ouras/STM32-Audio-Effects-Unit/board/LTspice/biased input amp with filter.asc

C1: cap; 1n
C2: cap; 10µ
C3: cap; 15µ
C4: cap; 1n
R1: res; 24k
R2: res; 220k
R3: res; 220k
R4: res; 1Meg
R5: res; 33k
R6: res; 2.4k
R7: res; 1.2k
U1: UniversalOpamp2
V1: voltage; 3.3
V2: voltage; ""; AC 100m 0
Named nets: 0, Vdd, out, in
.ac lin 1000 1 30k
