ouras/STM32-Audio-Effects-Unit/board/LTspice/output filter.asc

C1: cap; 2.2n
C2: cap; 10µ
C4: cap; 1n
R1: res; 4.3k
R4: res; 1Meg
R7: res; 3.3k
U1: UniversalOpamp2
V1: voltage; 3.3
V2: voltage; ""; AC 100m 0
Named nets: 0, Vdd, out, in
.ac lin 1000 1 30k
