ouras/STM32-Audio-Effects-Unit/board/LTspice/power.asc

D1: schottky
D2: schottky
M1: pmos
R1: res; 10k
R2: res; 1k
V1: voltage; 9
V2: voltage; 9
V3: voltage; 5
Named nets: 0, wall, bat, usb, out
.tran 1s startup
